dcowden/esp32_breakout_board/sdcard_shield/board_art/back_kerf.png

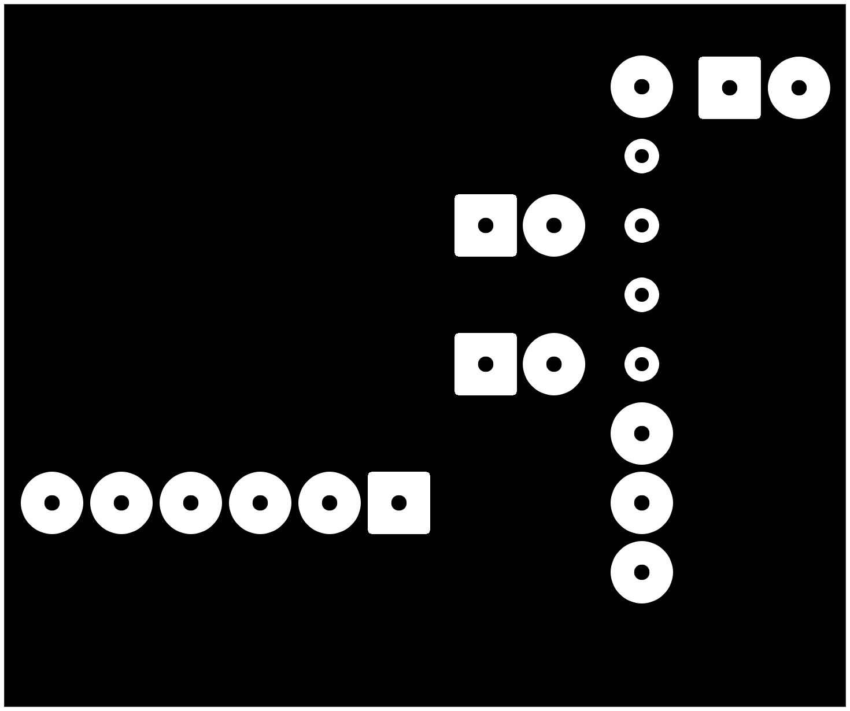
sdcard_shield/board_art/back_kerf.png
