dcowden/esp32_breakout_board/sdcard_shield/board_art/mask-back-kerf.png

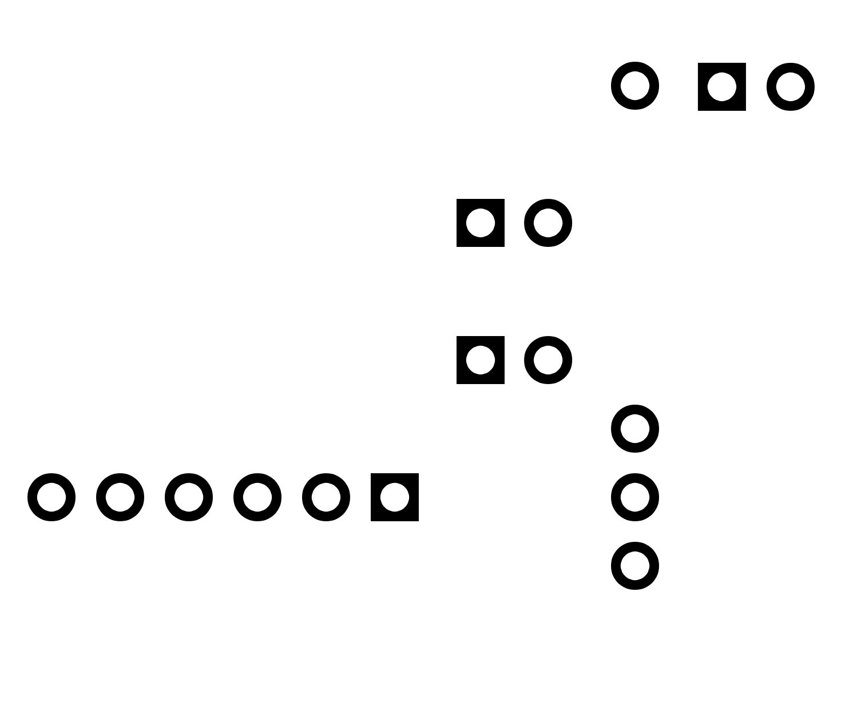
sdcard_shield/board_art/mask-back-kerf.png
