dcowden/esp32_breakout_board/sdcard_shield/board_art/cuts.dxf/sdcard_shield-User_Drawings.dxf

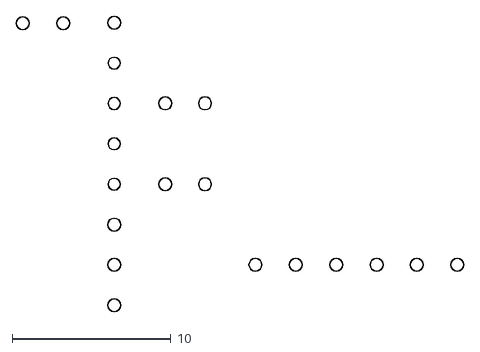
[picture p20: CAD file, 2025-12-20]
sdcard_shield/board_art/cuts.dxf/sdcard_shield-User_Drawings.dxf
28.2 x 18.6
